akaStanley/HTML_Accelerator/images/HTML-Accel_Spencer.jpg

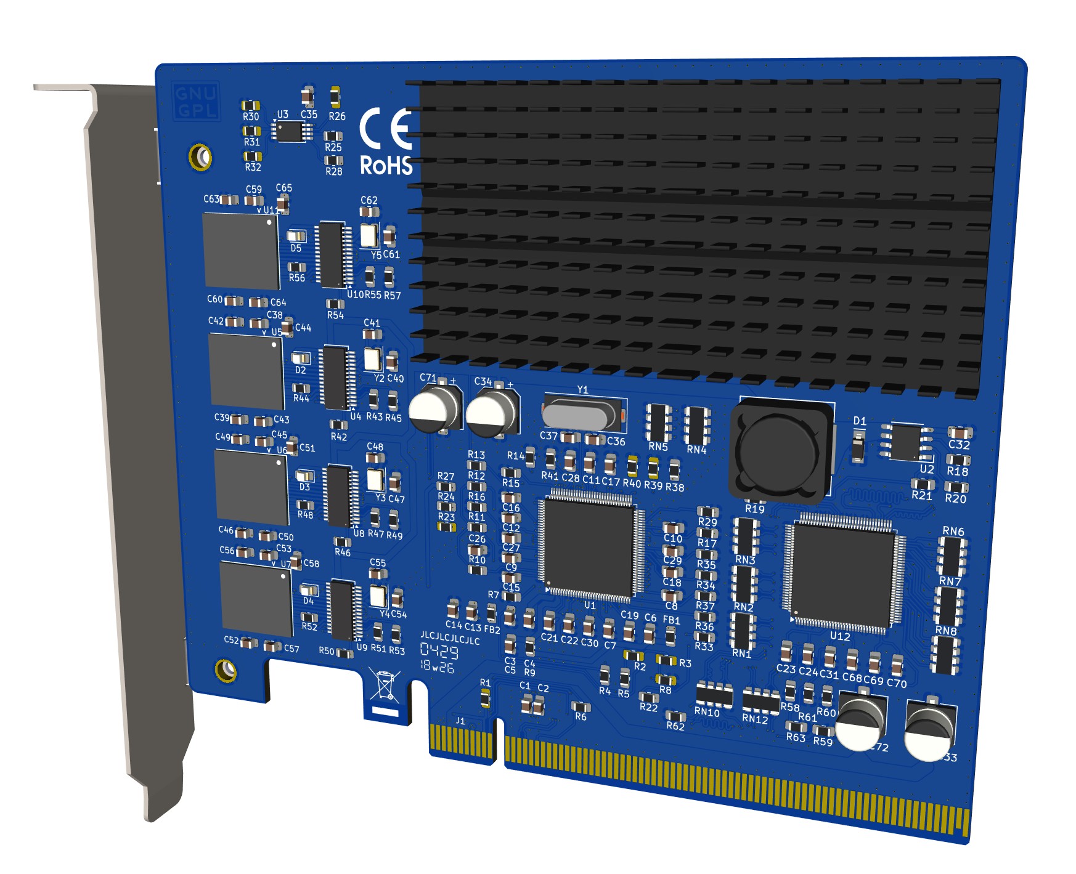
images/HTML-Accel_Spencer.jpg
