akaStanley/HTML_Accelerator/images/HTML-Accelerator-Card_Ninji.jpeg

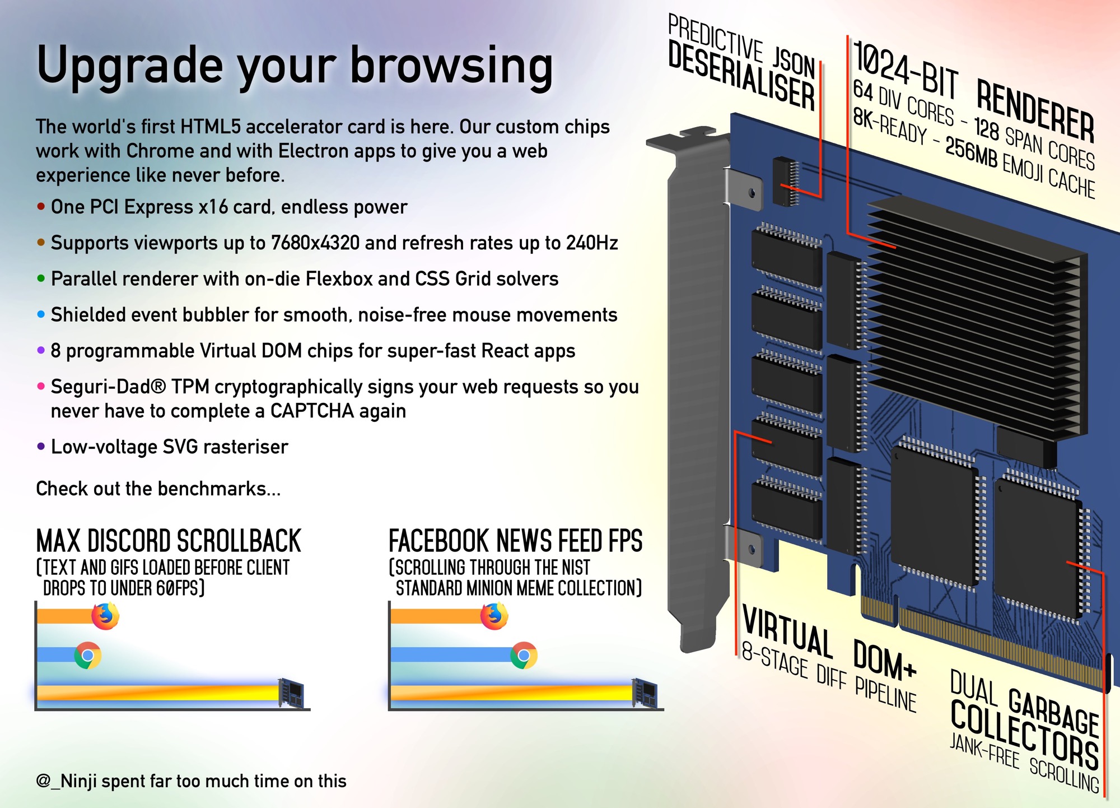
images/HTML-Accelerator-Card_Ninji.jpeg
