akaStanley/HTML_Accelerator/images/PCBLayout3.jpg

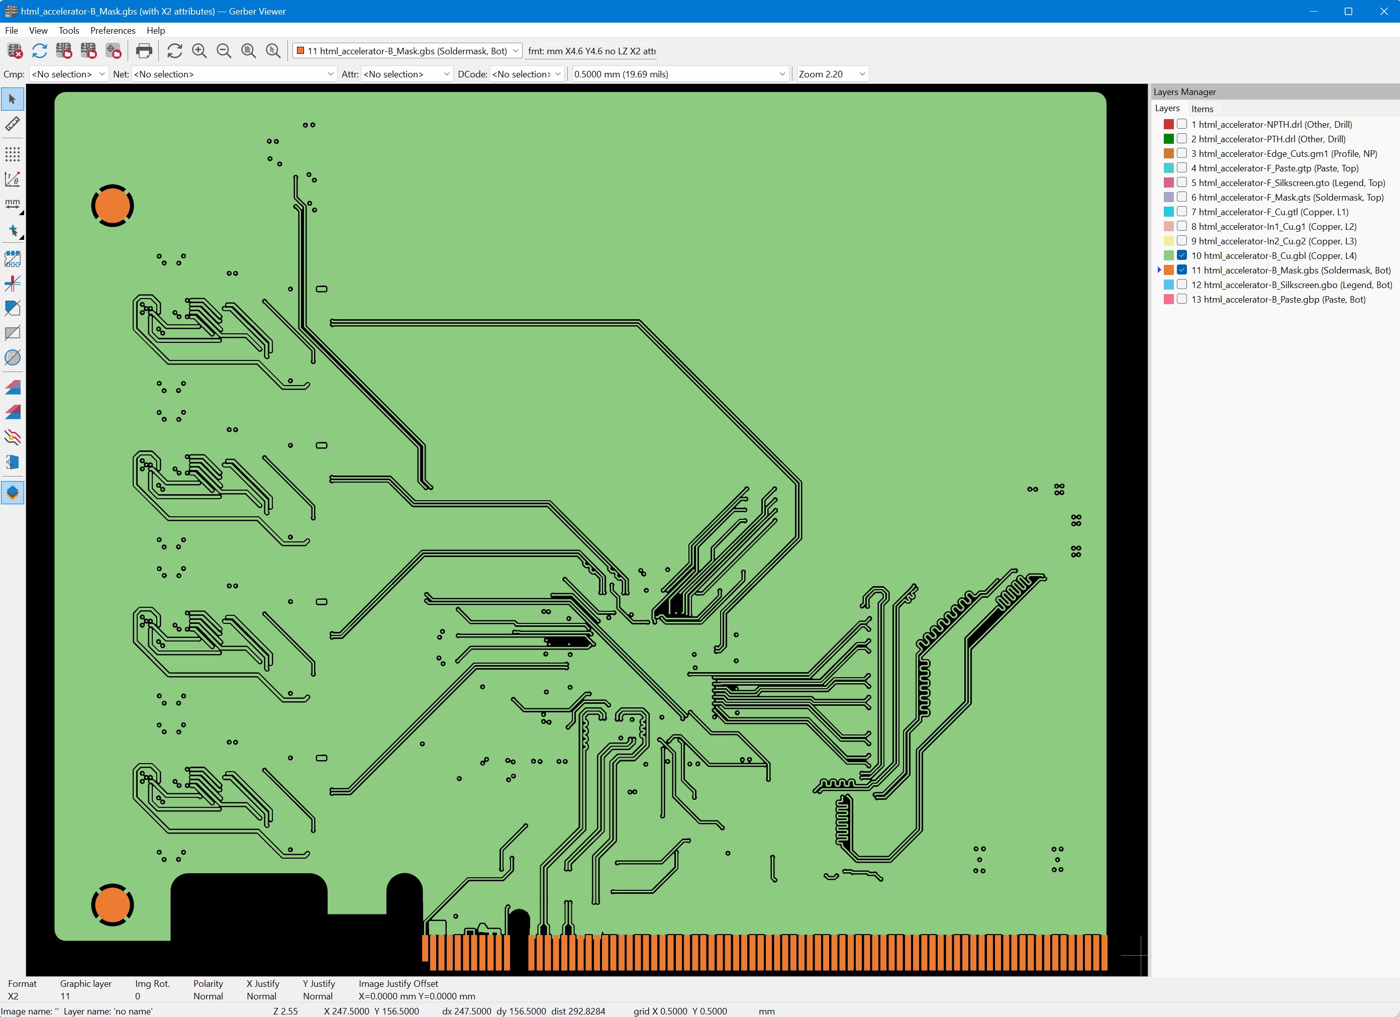
images/PCBLayout3.jpg
